system2neurotech/thermometer/assembly pictures/probe board with wires.jpg

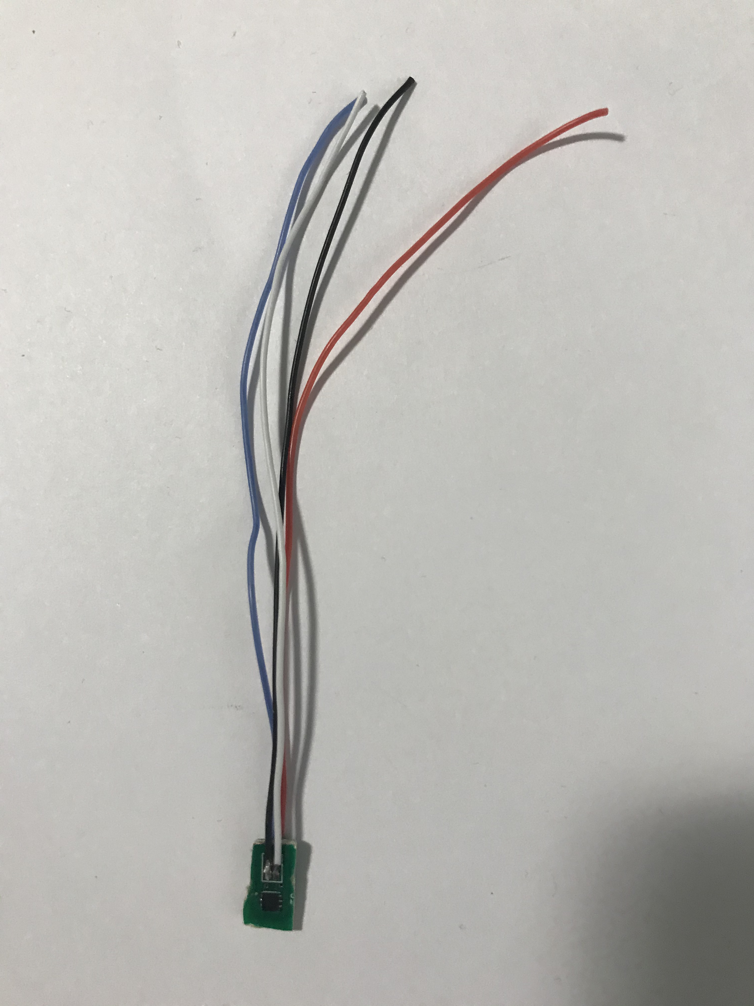
assembly pictures/probe board with wires.jpg
